JohannesWaltmann/bachelor_project/Casing/Exports/front.dxf

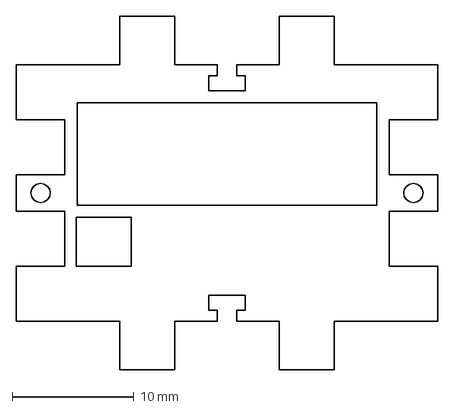
[picture p16: CAD file, 2021-03-11, an earlier design]
Casing/Exports/front.dxf
34.6 x 29.0 mm
