JohannesWaltmann/bachelor_project/Casing/Exports/right.dxf

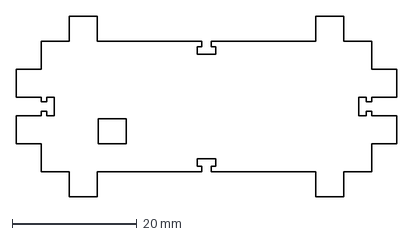
[picture p17: CAD file, 2021-03-11, an earlier design]
Casing/Exports/right.dxf
61.0 x 29.0 mm
