JohannesWaltmann/bachelor_project/Code_Tests/test_webserver/requirements.h

#include "Arduino.h"
#include "FS.h"

const int c = 261;
const int d = 294;
const int e = 329;
const int f = 349;
const int g = 391;
const int gS = 415;
const int a = 440;
const int aS = 466;
const int b = 494;
const int cH = 523;
const int cSH = 554;
const int dH = 587;
const int dSH = 622;
const int eH = 659;
const int fH = 698;
const int fSH = 740;
const int gH = 784;
const int gSH = 830;
const int aH = 880;

extern File file;

void listSD();

void wavHeader(byte* header, int wavSize);
